Makerfabs/Makerfabs-ESP32-S3-SPI-TFT-with-Touch/example/image_display/2.bmp

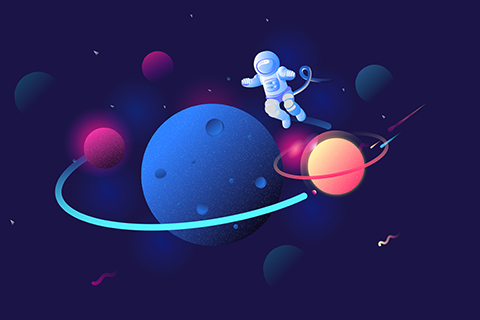
example/image_display/2.bmp
