Makerfabs/Makerfabs-ESP32-S3-SPI-TFT-with-Touch/example/image_display/4.bmp

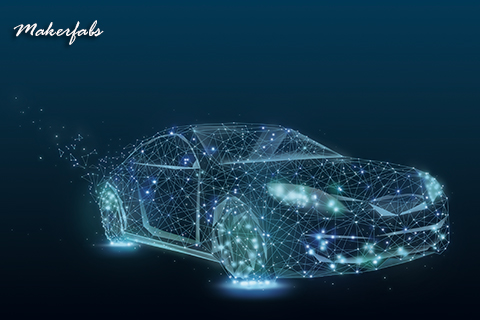
example/image_display/4.bmp
