Makerfabs/Makerfabs-ESP32-S3-SPI-TFT-with-Touch/IDF/matouch/main/firmware/3-5-ili9488-ft6236/assets/7.jpg

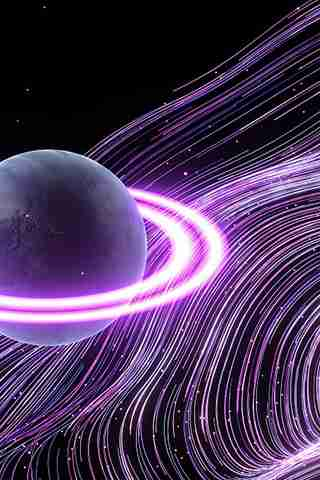
IDF/matouch/main/firmware/3-5-ili9488-ft6236/assets/7.jpg
